bravecorvus/prometheus/assets/golang.png

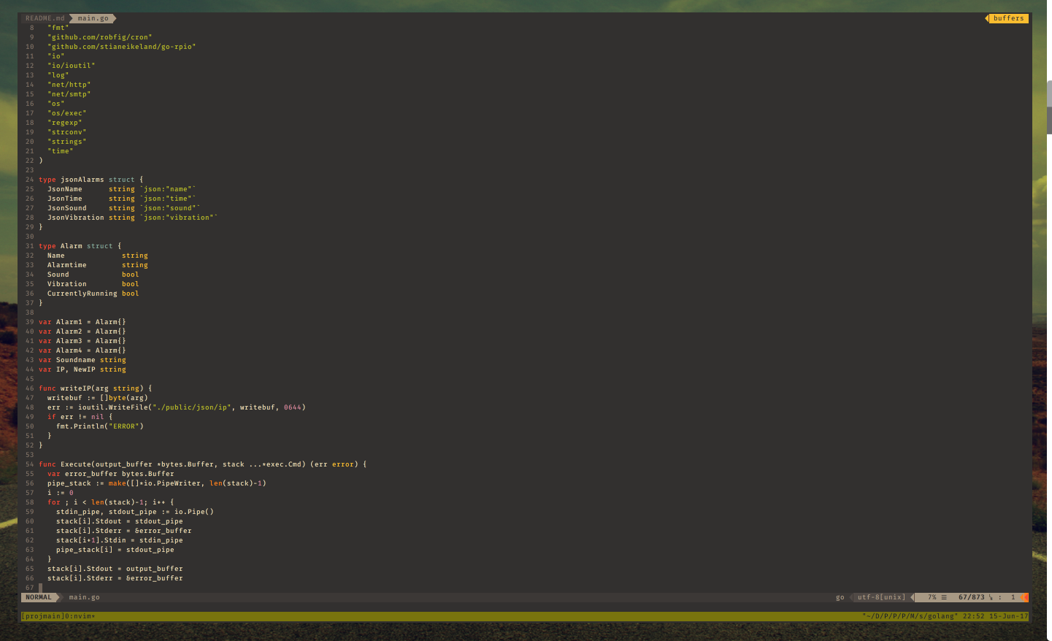
assets/golang.png
