bravecorvus/prometheus/assets/hackadaycover2.jpg

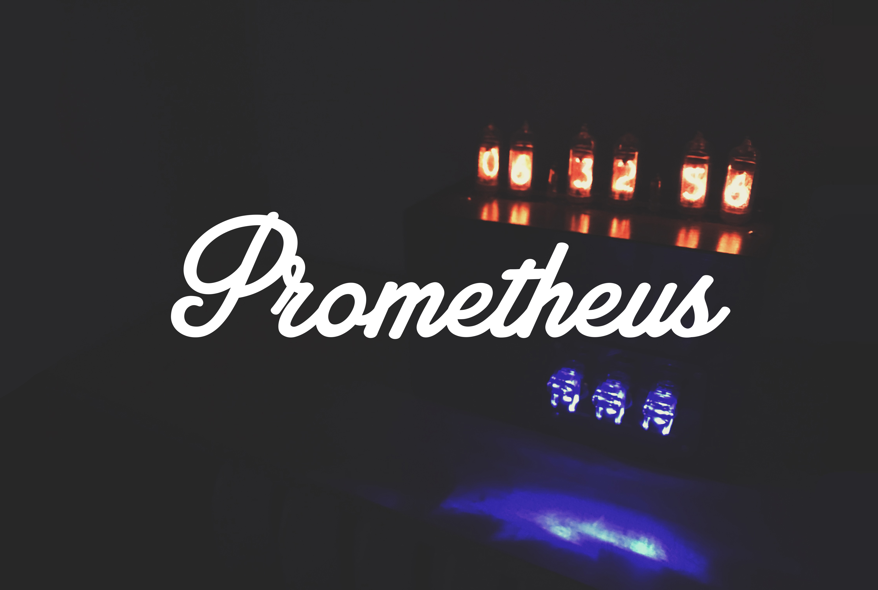
assets/hackadaycover2.jpg
