bravecorvus/prometheus/assets/hackadaycover.jpg

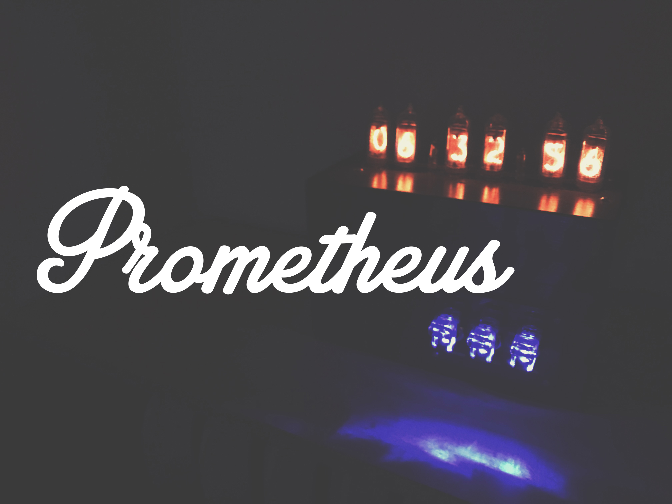
assets/hackadaycover.jpg
