bravecorvus/prometheus/assets/IMG_1782.JPG

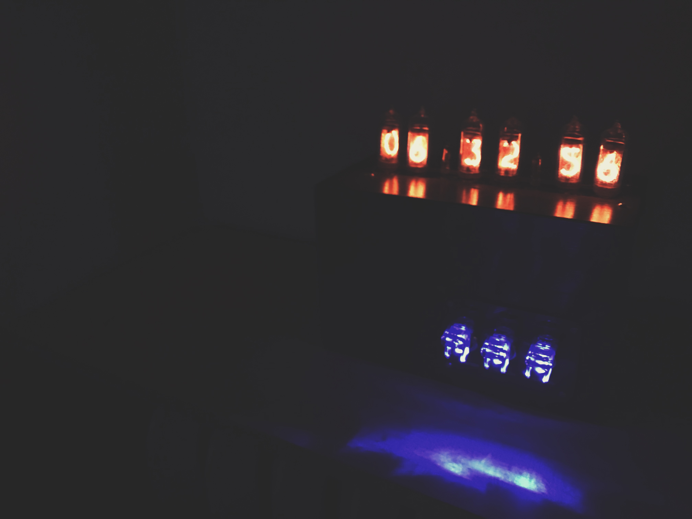
assets/IMG_1782.JPG
