bravecorvus/prometheus/assets/rpi.jpg

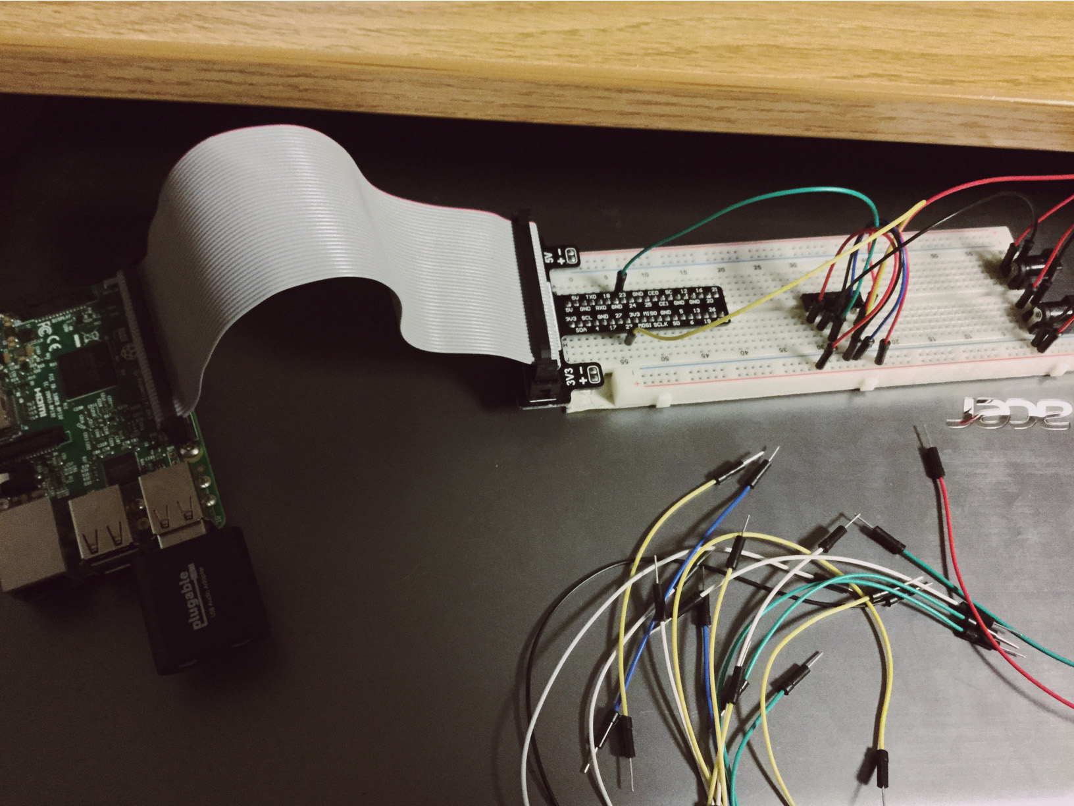
assets/rpi.jpg
