bravecorvus/prometheus/assets/solderusb.jpg

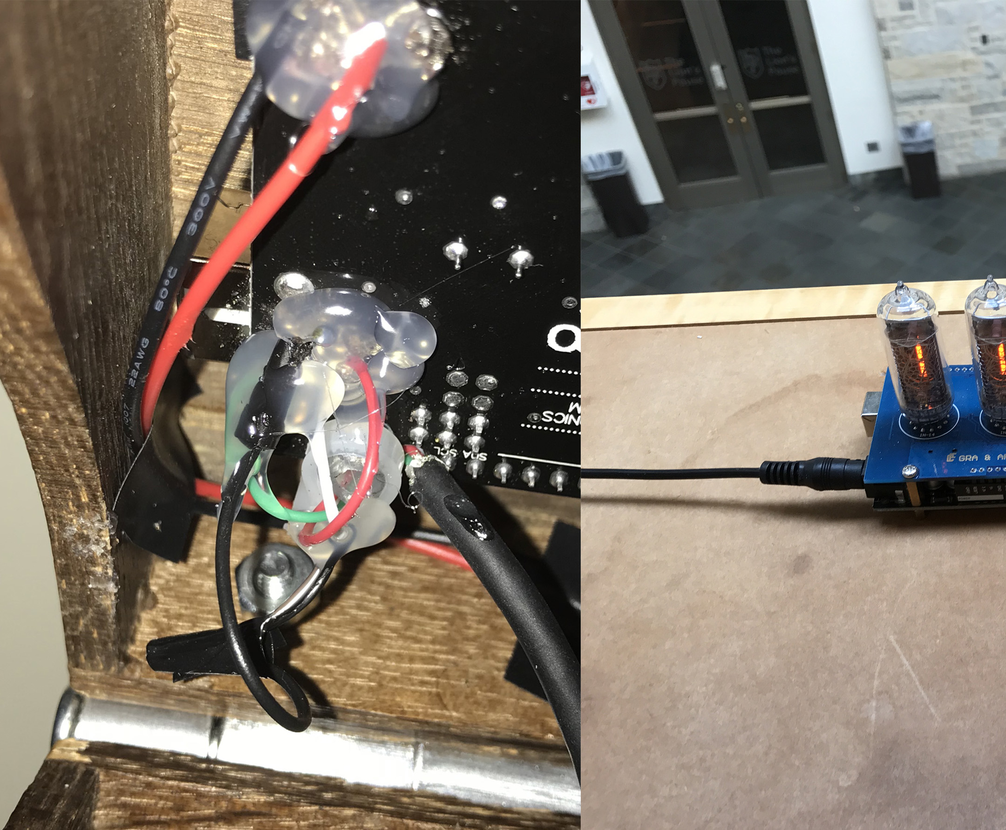
assets/solderusb.jpg
